oleksiikutuzov/flipperzero-flasher-board/images/photo_1.jpg

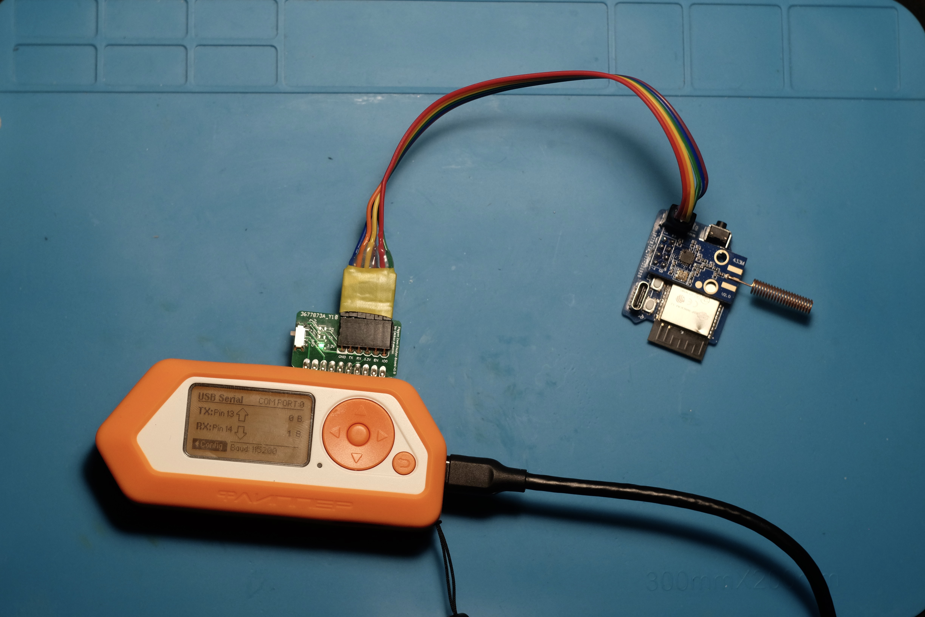
images/photo_1.jpg
